sbelectronics/ps2-tandy/tandy_scancode_map.h

const char scancode_map[128] PROGMEM = {0,67,0,63,61,59,60,90,0,68,66,64,62,15,0,0,0,56,42,0,29,16,2,0,0,0,44,31,30,17,3,0,0,46,45,32,18,5,4,0,0,57,47,33,20,19,6,0,0,49,48,35,34,21,7,0,0,0,50,36,22,8,9,0,0,51,37,23,24,11,10,0,0,52,53,38,39,25,12,0,0,0,40,0,26,13,0,0,58,54,28,27,0,0,0,0,0,0,0,0,0,0,14,0,0,79,0,75,71,0,0,0,82,86,80,76,77,72,1,69,89,0,81,12,0,73,70,0};
const char extcode_map[128] PROGMEM = {0,0,0,0,0,0,0,0,0,0,0,0,0,0,0,0,0,56,0,0,56,0,0,0,0,0,0,0,0,0,0,0,0,0,0,0,0,0,0,0,0,0,0,0,0,0,0,0,0,0,0,0,0,0,0,0,0,0,0,0,0,0,0,0,0,0,0,0,0,0,0,0,0,0,53,0,0,0,0,0,0,0,0,0,0,0,0,0,0,0,87,0,0,0,0,0,0,0,0,0,0,0,0,0,0,0,0,43,88,0,0,0,85,83,74,0,78,41,0,0,0,0,0,0,0,0,84,0};
