sbelectronics/ps2-tandy/tandy_scancode_list.py

from ps2_scancode_list import *

tandy_codes=[
  (1, F1, 0x3B),
  (2, F2, 0x3C),
  (3, F3, 0x3D),
  (4, F4, 0x3E),
  (5, F5, 0x3F),
  (6, F6, 0x40),
  (7, F7, 0x41),
  (8, F8, 0x42),
  (9, F9, 0x43),
  (10, F10, 0x44),
  (11, F11, 0x59),
  (12, F12, 0x5A),
  (13, INS, 0x55),
  (14, DEL, 0x53),
  (15, BREAK, 0x54),
  (16, ESC, 0x01),
  (17, '1', 0x02),
  (18, '2', 0x03),
  (19, '3', 0x04),
  (20, '4', 0x05),
  (21, '5', 0x06),
  (22, '6', 0x07),
  (23, '7', 0x08),
  (24, '8', 0x09),
  (25, '9', 0x0A),
  (26, '0', 0x0B),
  (27, '-', 0x0C),
  (28, '=', 0x0D),
  (29, BS, 0x0E),
  (30, LALT, 0x38),
  (31, PRINTSCR, 0x37),
  (32, KP7, 0x47),
  (33, KP8, 0x48),
  (34, KP9, 0x49),
  (35, TAB, 0x0F),
  (36, 'Q', 0x10),
  (37, 'W', 0x11),
  (38, 'E', 0x12),
  (39, 'R', 0x13),
  (40, 'T', 0x14),
  (41, 'Y', 0x15),
  (42, 'U', 0x16),
  (43, 'I', 0x17),
  (44, 'O', 0x18),
  (45, 'P', 0x19),
  (46, '{', 0x1A),
  (47, '}', 0x1B),
  (48, SCROLL, 0x46),
  (49, NUM, 0x45),
  (50, KP4, 0x4B),
  (51, KP5, 0x4C),
  (52, KP6, 0x4D),
  (53, LCTRL, 0x1D),
  (54, 'A', 0x1E),
  (55, 'S', 0x1F),
  (56, 'D', 0x20),
  (57, 'F', 0x21),
  (58, 'G', 0x22),
  (59, 'H', 0x23),
  (60, 'J', 0x24),
  (61, 'K', 0x25),
  (62, 'L', 0x26),
  (63, ';', 0x27),
  (64, '\'', 0x28),
  (65, ENTER, 0x1C),
  (66, UARR, 0x29),
  (67, HOME, 0x58),
  (68, KP1, 0x4F),
  (69, KP2, 0x50),
  (70, KP3, 0x51),
  (71, CAPSLOCK, 0x3A),
  (72, LSHIFT, 0x2A),
  (73, 'Z', 0x2C),
  (74, 'X', 0x2D),
  (75, 'C', 0x2E),
  (76, 'V', 0x2F),
  (77, 'B', 0x30),
  (78, 'N', 0x31),
  (79, 'M', 0x32),
  (80, ',', 0x33),
  (81, '.', 0x34),
  (82, '/', 0x35),
  (83, RSHIFT, 0x36),
  (84, LARR, 0x2B),
  (85, DARR, 0x4A),
  (86, RARR, 0x4E),
  (87, KP0, 0x52),
  (88, KPDOT, 0x56),
  (89, KPENTER, 0x57),
  (90, SPACE, 0x39)
]
